BrentGG/1EAI-PO/images/IMG_20220601_004026.jpg

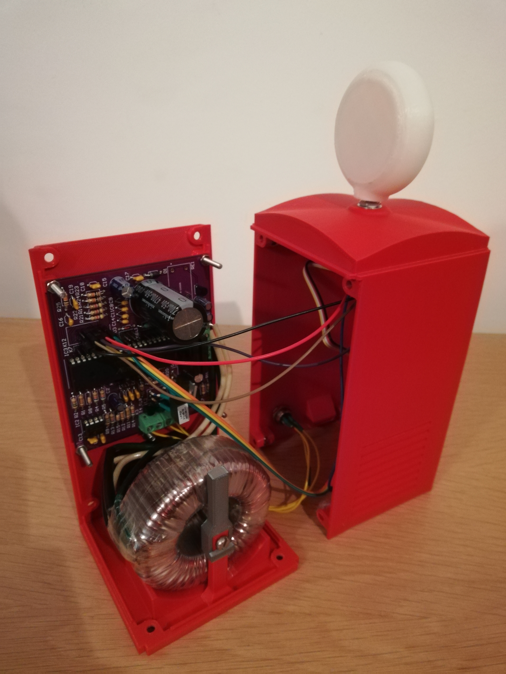
images/IMG_20220601_004026.jpg
