BrentGG/1EAI-PO/images/IMG_20220601_004032.jpg

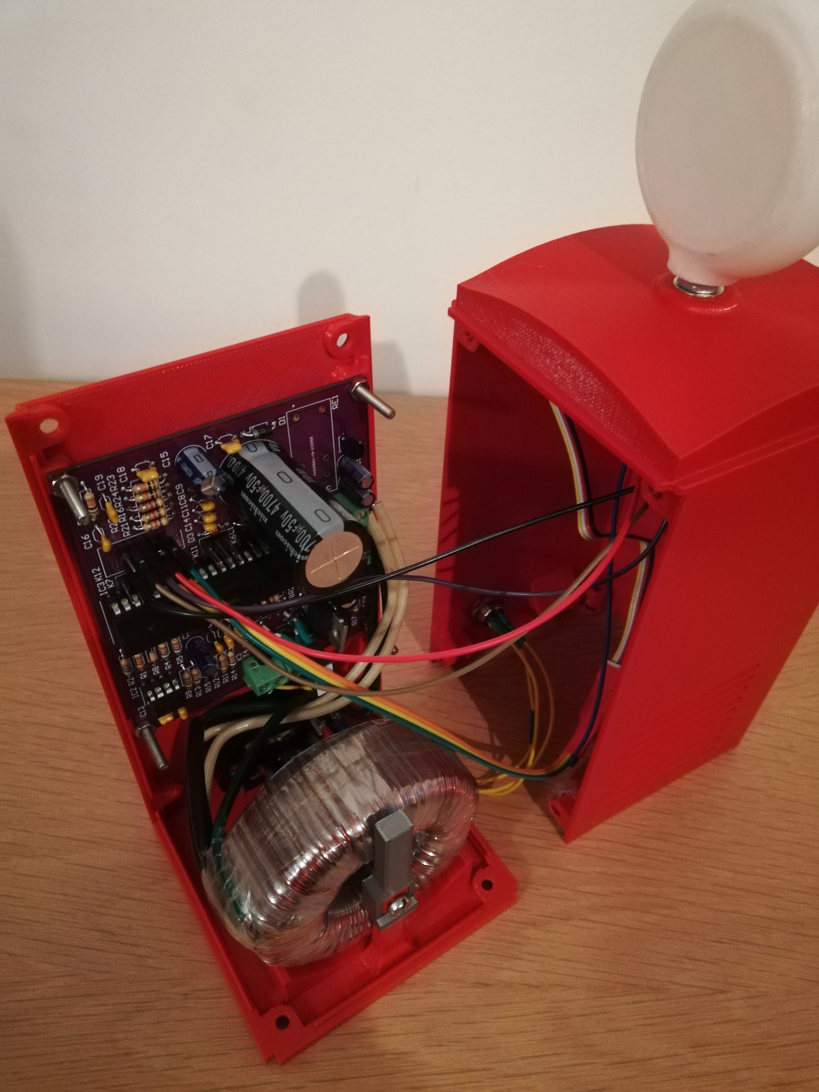
images/IMG_20220601_004032.jpg
