BrentGG/1EAI-PO/images/IMG_20220601_013259.jpg

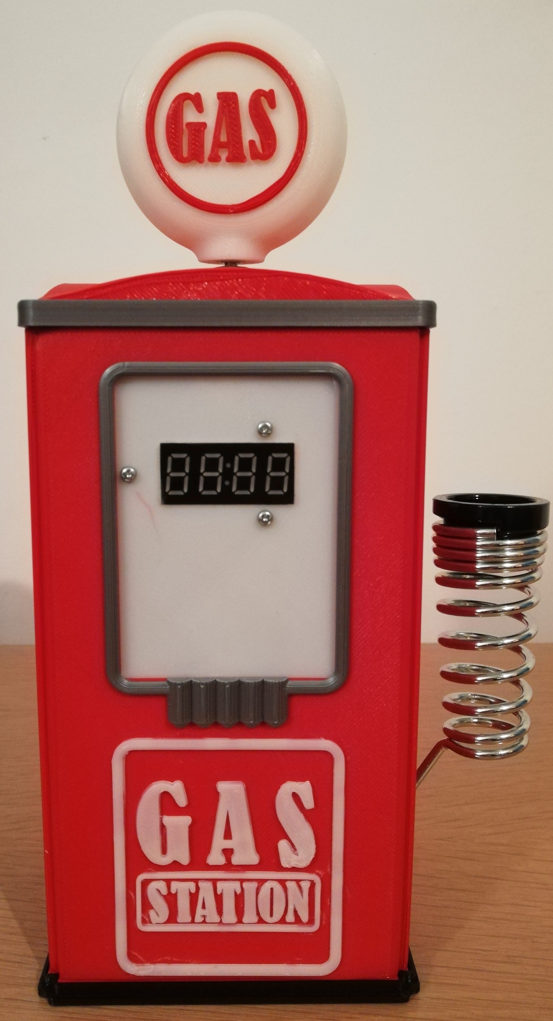
images/IMG_20220601_013259.jpg
