BrentGG/1EAI-PO/images/IMG_20220601_013333_1.jpg

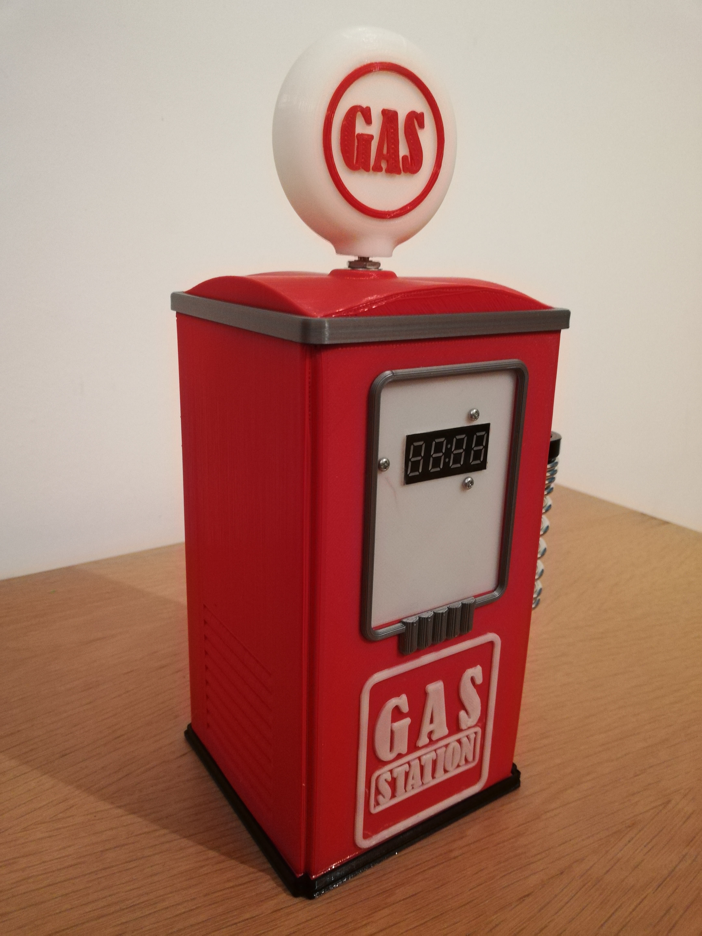
images/IMG_20220601_013333_1.jpg
